raulgr-h/stm32-environmental-data-logger/docs/images/Waveforms/3.3V Rail Startup Response - Waveforms.png

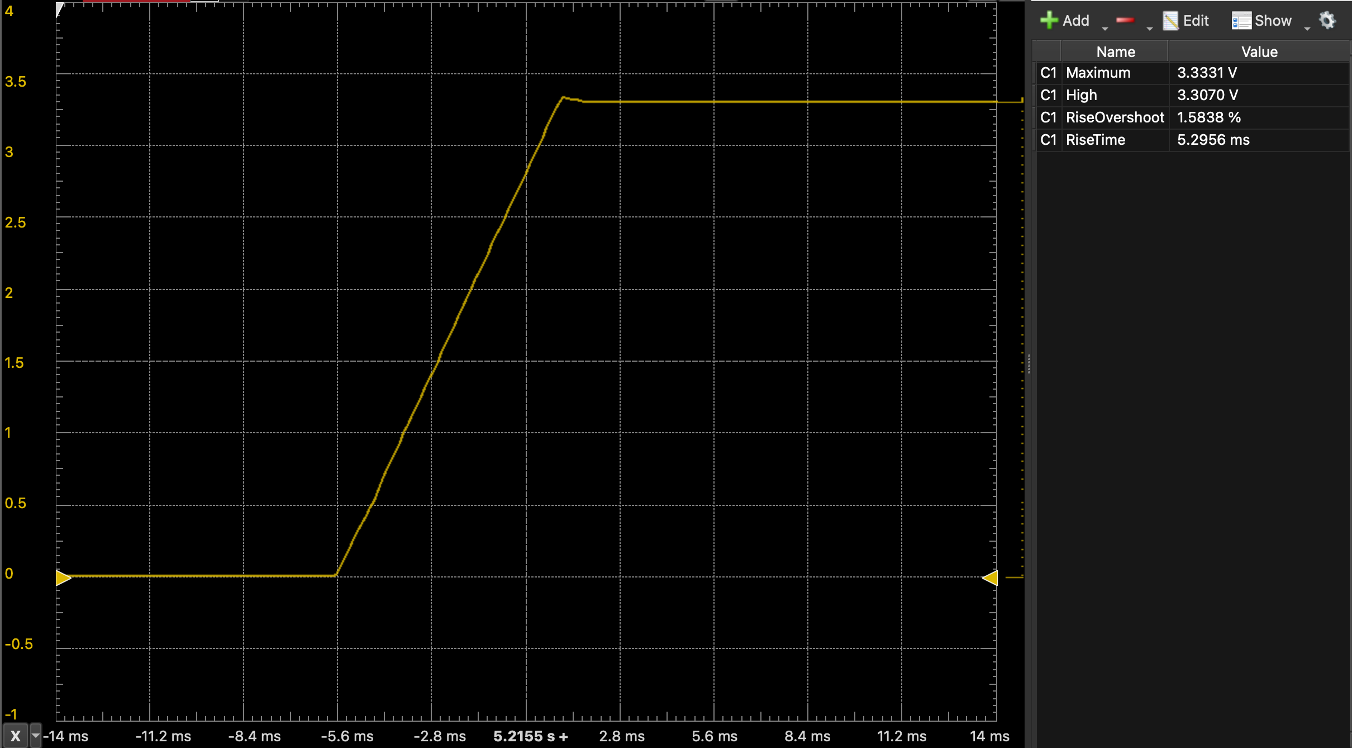
docs/images/Waveforms/3.3V Rail Startup Response - Waveforms.png
