raulgr-h/stm32-environmental-data-logger/docs/images/Waveforms/BTN-Triggered Sampling (Zoomed) - Waveforms.png

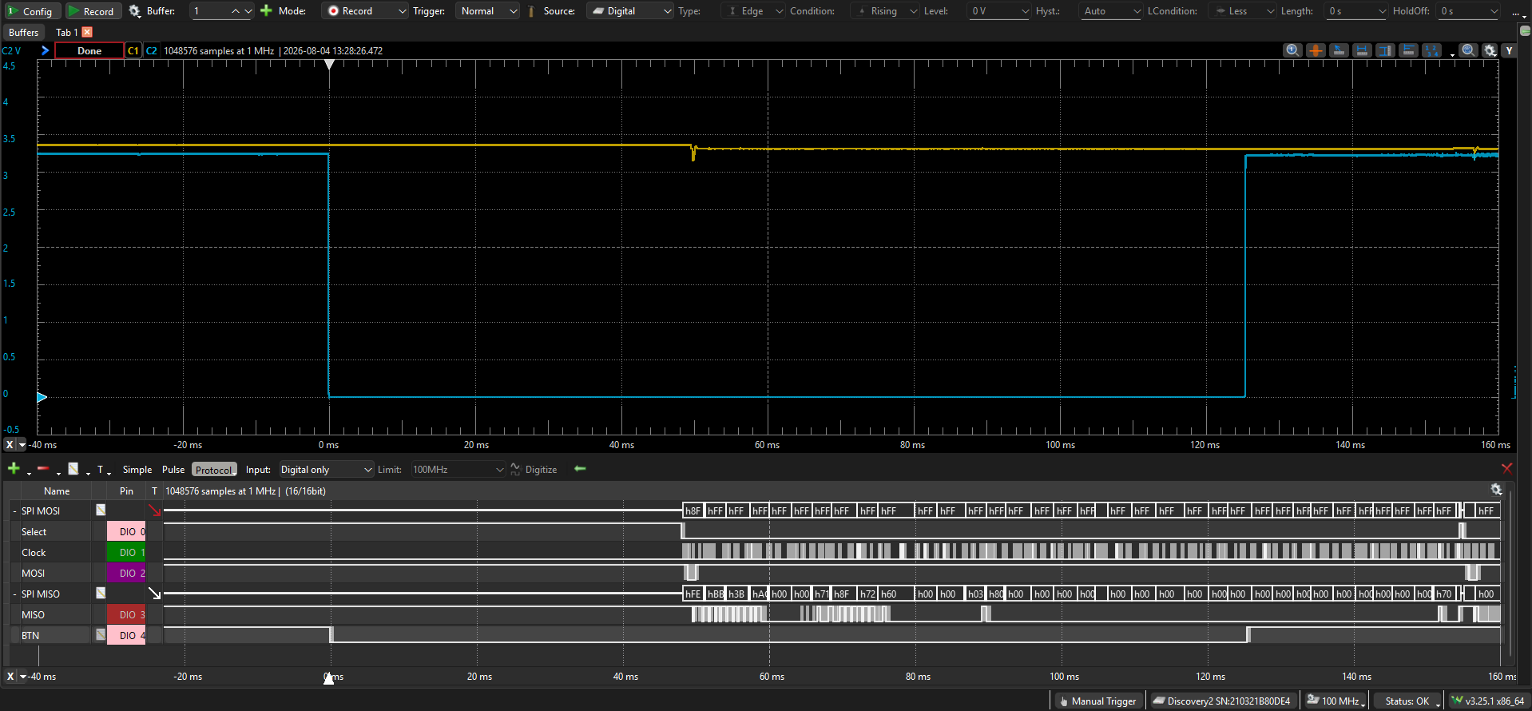
docs/images/Waveforms/BTN-Triggered Sampling (Zoomed) - Waveforms.png
