raulgr-h/stm32-environmental-data-logger/docs/images/Waveforms/BTN-Triggered Sampling - Waveforms.png

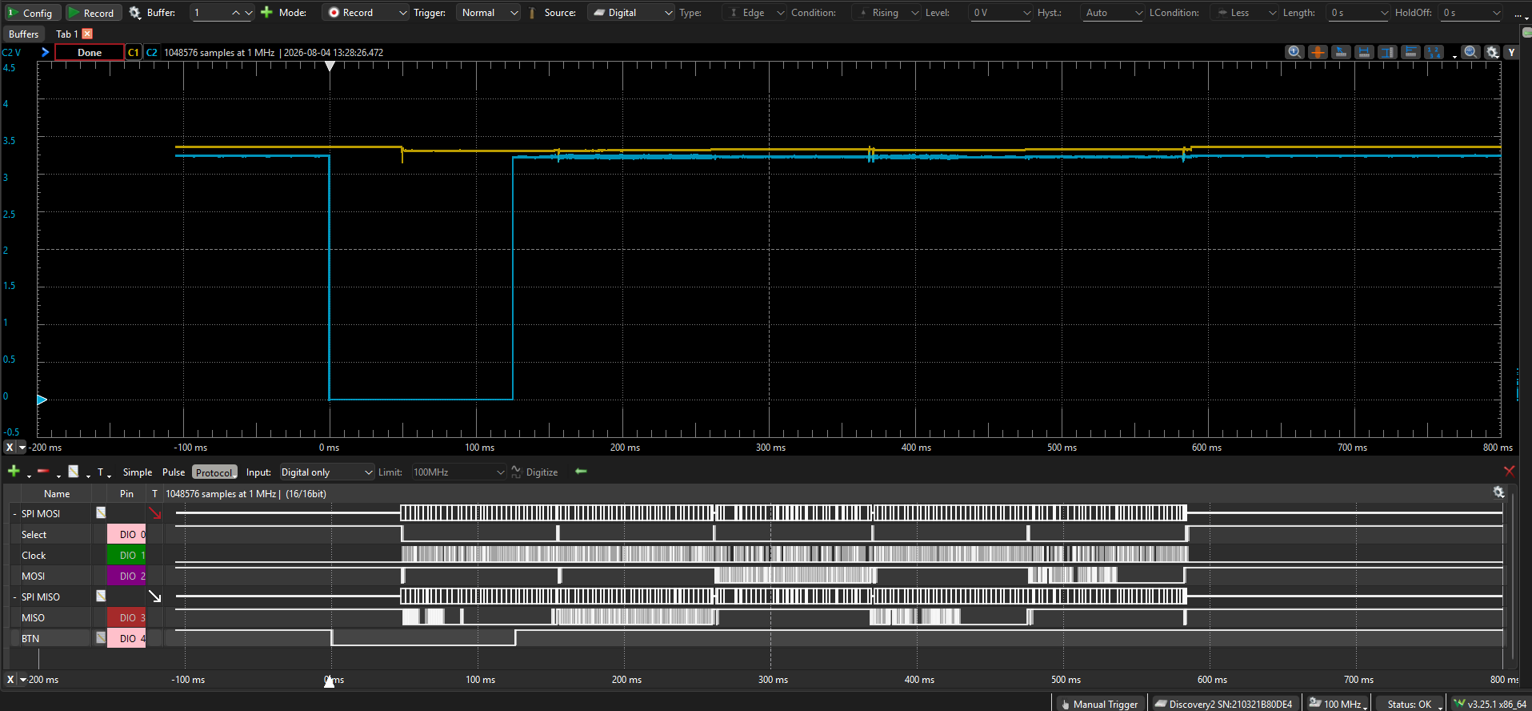
docs/images/Waveforms/BTN-Triggered Sampling - Waveforms.png
