raulgr-h/stm32-environmental-data-logger/docs/images/Waveforms/SD Write Supply Stability.png

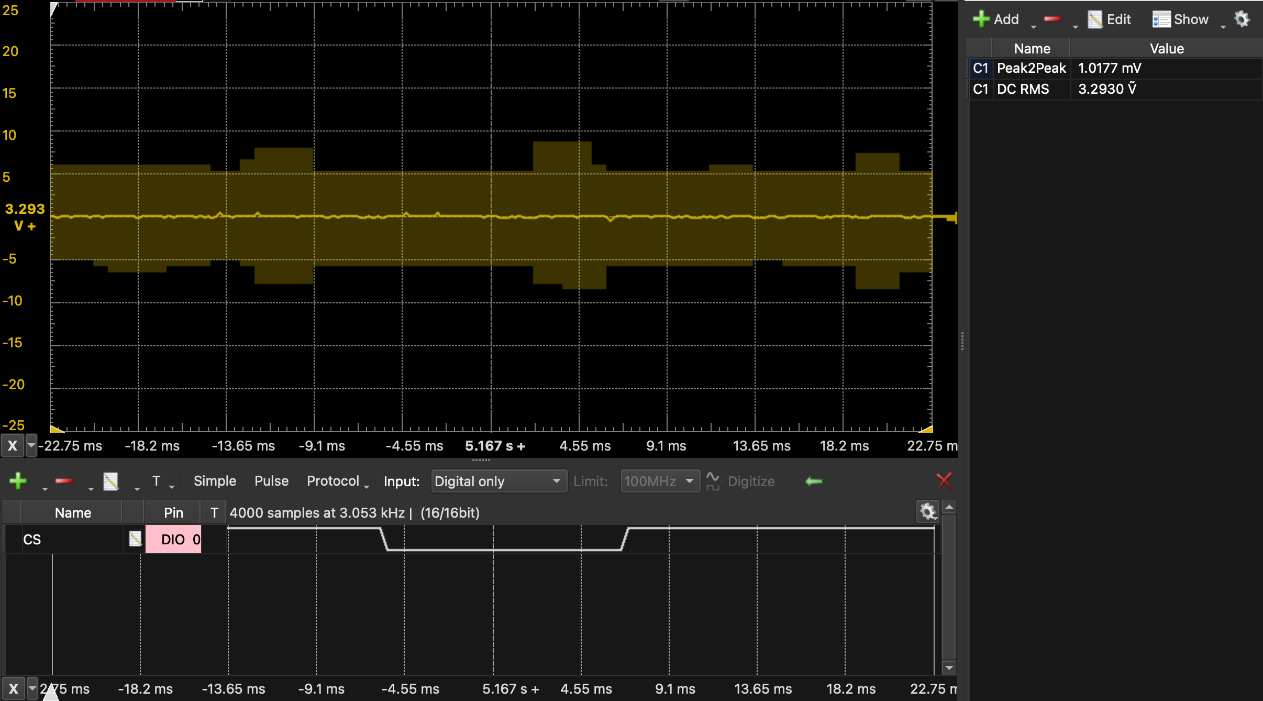
docs/images/Waveforms/SD Write Supply Stability.png
