raulgr-h/stm32-environmental-data-logger/test/raw-data/ate/20260821_105910_DIO0_996.0ohm_100ms_R1.csv

time_s | ch1_raw_V | vbat_V
0.0 | -0.0007365323933453994 | 3.036828996491051
1e-05 | -0.0007365323933453994 | 3.040490650164099
2e-05 | -0.000397304146647373 | 3.036828996491051
3e-05 | -0.000397304146647373 | 3.036828996491051
4e-05 | -0.0007365323933453994 | 3.040490650164099
5e-05 | -0.000397304146647373 | 3.040490650164099
6e-05 | -0.000397304146647373 | 3.040490650164099
7e-05 | -0.000397304146647373 | 3.040490650164099
8e-05 | -0.0007365323933453994 | 3.040490650164099
9e-05 | -0.000397304146647373 | 3.040490650164099
0.0001 | -0.000397304146647373 | 3.040490650164099
0.00011 | -0.0007365323933453994 | 3.040490650164099
0.00012 | -0.000397304146647373 | 3.040490650164099
0.00013 | -0.0007365323933453994 | 3.036828996491051
0.00014 | -0.0007365323933453994 | 3.040490650164099
0.00015 | -0.0007365323933453994 | 3.036828996491051
0.00016 | -0.0007365323933453994 | 3.040490650164099
0.00017 | -0.0007365323933453994 | 3.040490650164099
0.00018 | -0.000397304146647373 | 3.036828996491051
0.00019 | -0.000397304146647373 | 3.040490650164099
0.0002 | -0.0007365323933453994 | 3.040490650164099
0.00021 | -0.000397304146647373 | 3.040490650164099
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
