raulgr-h/stm32-environmental-data-logger/test/raw-data/ate/20260821_110216_DIO0_996.0ohm_10ms_R1.csv

time_s | ch1_raw_V | vbat_V
0.0 | -5.8075899949346695e-05 | 3.044152303837147
1e-05 | -0.000397304146647373 | 3.0478139575101952
2e-05 | -5.8075899949346695e-05 | 3.0478139575101952
3e-05 | -5.8075899949346695e-05 | 3.0478139575101952
4e-05 | -5.8075899949346695e-05 | 3.044152303837147
5e-05 | -5.8075899949346695e-05 | 3.0478139575101952
6e-05 | -5.8075899949346695e-05 | 3.044152303837147
7e-05 | -5.8075899949346695e-05 | 3.0478139575101952
8e-05 | 0.00028115234674867964 | 3.044152303837147
9e-05 | -5.8075899949346695e-05 | 3.044152303837147
0.0001 | -5.8075899949346695e-05 | 3.044152303837147
0.00011 | -5.8075899949346695e-05 | 3.044152303837147
0.00012 | -5.8075899949346695e-05 | 3.0478139575101952
0.00013 | 0.00028115234674867964 | 3.044152303837147
0.00014 | -0.000397304146647373 | 3.0478139575101952
0.00015 | -5.8075899949346695e-05 | 3.044152303837147
0.00016 | 0.00028115234674867964 | 3.0478139575101952
0.00017 | -5.8075899949346695e-05 | 3.0478139575101952
0.00018 | -0.000397304146647373 | 3.0478139575101952
0.00019 | -5.8075899949346695e-05 | 3.0478139575101952
0.0002 | -5.8075899949346695e-05 | 3.0478139575101952
0.00021 | -5.8075899949346695e-05 | 3.0478139575101952
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
