raulgr-h/stm32-environmental-data-logger/docs/images/BTN-Triggered Sampling CSV Results.png

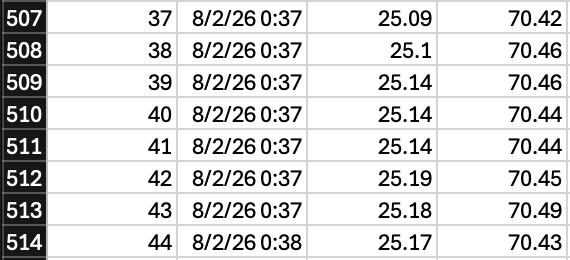
docs/images/BTN-Triggered Sampling CSV Results.png
