raulgr-h/stm32-environmental-data-logger/test/oscilloscope/environmental-logger-shunt-waveform_zoomed.png

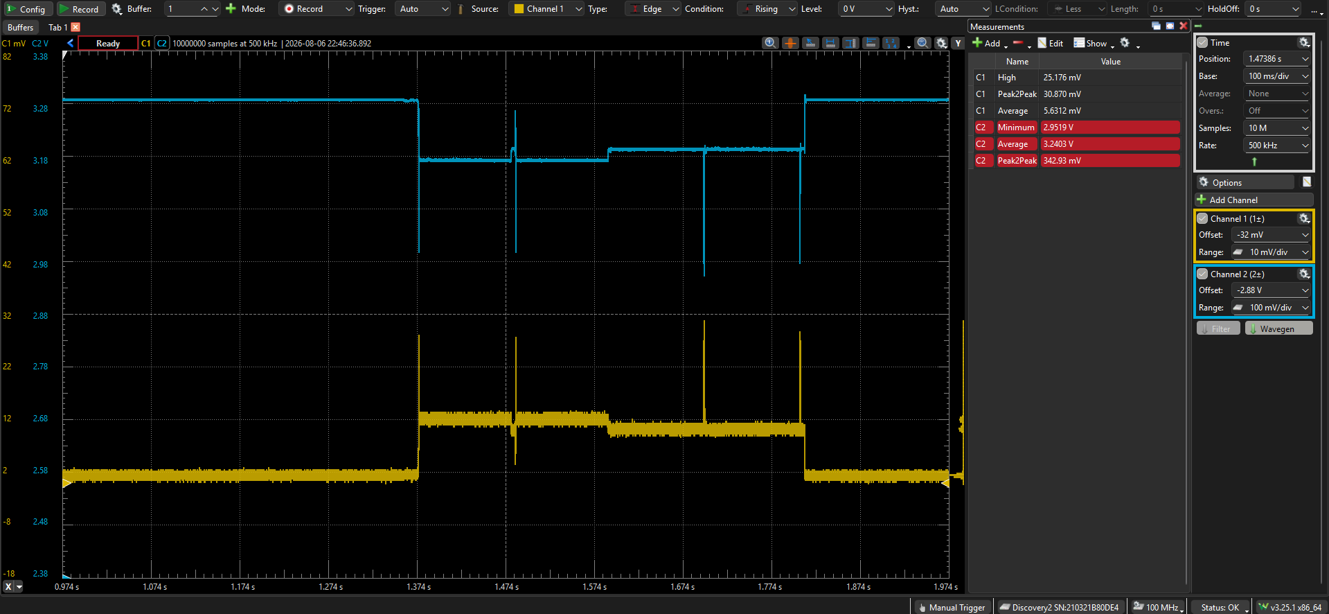
test/oscilloscope/environmental-logger-shunt-waveform_zoomed.png
