raulgr-h/stm32-environmental-data-logger/docs/images/Debugger Expressions/BTN-Triggered Sampling Expressions.png

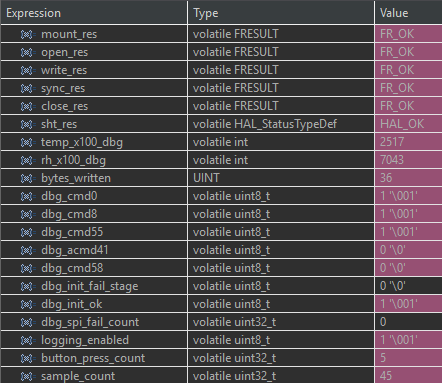
docs/images/Debugger Expressions/BTN-Triggered Sampling Expressions.png
