raulgr-h/stm32-environmental-data-logger/docs/images/Debugger Expressions/Debug Expressions.png

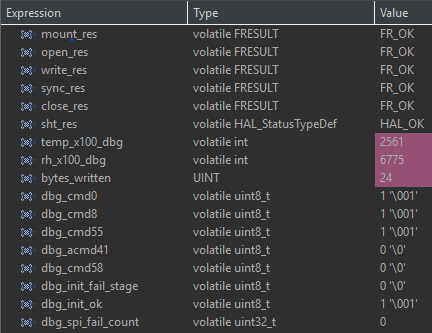
docs/images/Debugger Expressions/Debug Expressions.png
